medibrick2025/Peltier-design/GUI/GUI_DGUS/32/00.bmp

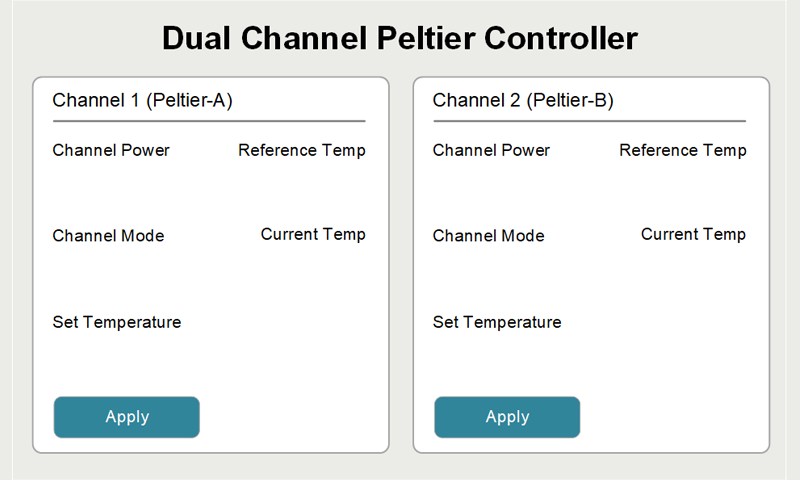
GUI/GUI_DGUS/32/00.bmp
