medibrick2025/Peltier-design/GUI/GUI_DGUS/32/01.bmp

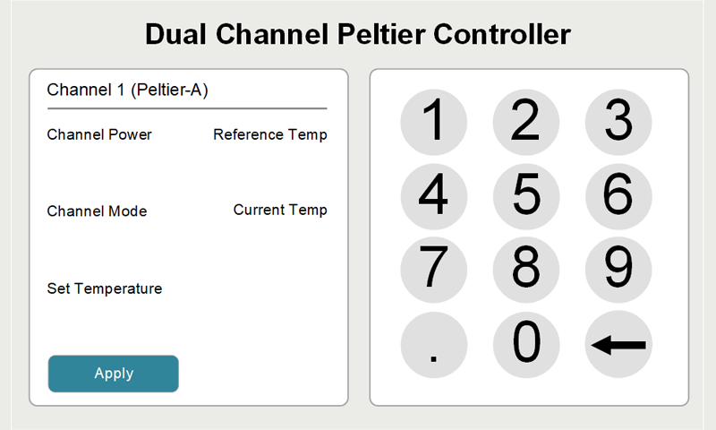
GUI/GUI_DGUS/32/01.bmp
