medibrick2025/Peltier-design/Assembly_and_instructions/Electrical_assembly_instructions.jpg

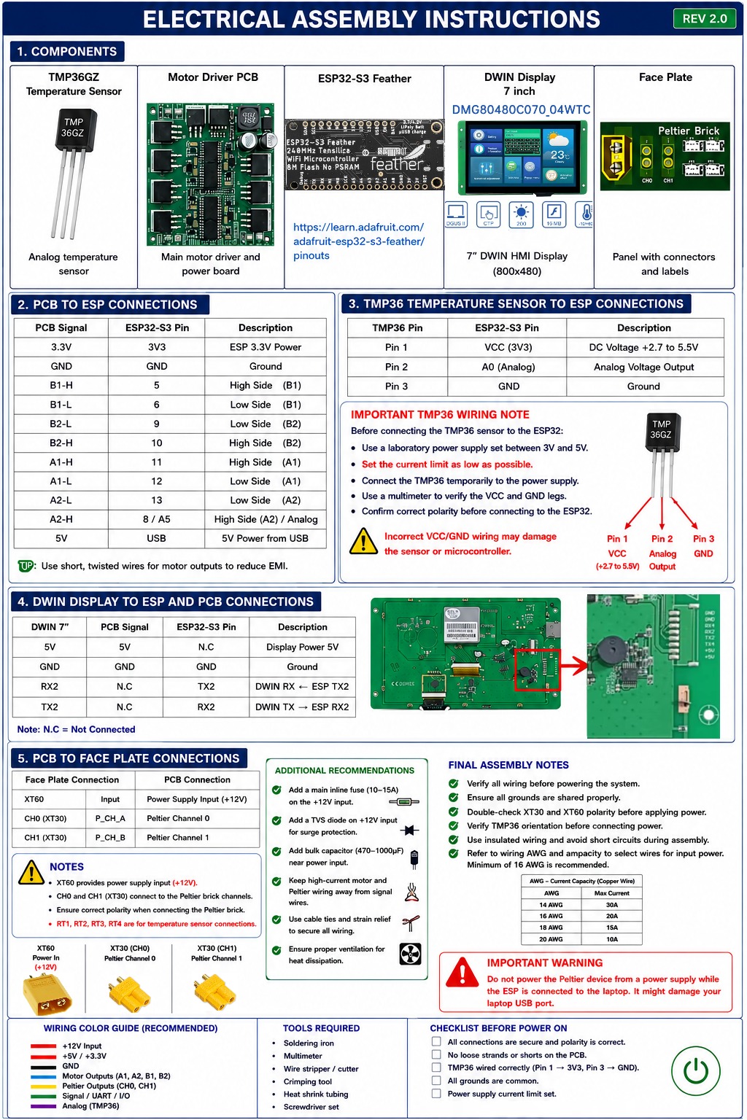
Assembly_and_instructions/Electrical_assembly_instructions.jpg
